joergenfriis/Steam-Engine-Simulator/Execute/damptabel.py

# damptabel.py
#
# Damptabel = [p (bar abs), tm (0C), v" (m3/kg), h' (kJ/kg), h" (kJ/kg)] (SI)
#
# Joergen Friis 25.01.2018
#########################################################################

damptabel = [
    [0.01, 6.9, 129.2, 29.34, 2514.4],
    [0.02, 17.5, 67.01, 73.46, 2533.6],
    [0.04, 28.9, 34.80, 121.41, 2554.5],
    [0.06, 36.2, 23.74, 151.50, 2567.5],
    [0.08, 41.5, 18.10, 173.86, 2577.1],
    [0.1, 45.8, 14.67, 191.83, 2584.8],
    [0.12, 49.4, 12.36, 206.94, 2591.2],
    [0.15, 54.0, 10.02, 225.97, 2599.2],
    [0.2, 60.1, 7.650, 251.45, 2609.9],
    [0.25, 65.0, 6.204, 271.99, 2618.3],
    [0.3, 69.1, 5.229, 289.30, 2625.4],
    [0.35, 72.7, 4.786, 304.30, 2631.5],
    [0.4, 75.9, 3.993, 317.65, 2636.9],
    [0.5, 81.3, 3.240, 340.56, 2646.0],
    [0.6, 85.9, 2.732, 359.93, 2653.6],
    [0.7, 90.0, 2.365, 376.77, 2660.1],
    [0.8, 93.5, 2.087, 391.72, 2665.8],
    [0.9, 96.7, 1.869, 405.21, 2670.9],
    [1, 99.6, 1.694, 417.51, 2675.4],
    [1.2, 104.8, 1,428, 439.36, 2683.4],
    [1.4, 109.3, 1.236, 458.42, 2690.3],
    [1.6, 113.3, 1.091, 475.38, 2696.2],
    [1.8, 116.9, 0.9772, 490.70, 2701.5],
    [2, 120.2, 0.8854, 504.70, 2706.3],
    [2.2, 123.3, 0.8098, 517.62, 2710.6],
    [2.4, 126.1, 0.7465, 529.64, 2714.5],
    [2.6, 128.7, 0.6925, 540.87, 2718.2],
    [2.8, 131.2, 0.6460, 551.44, 2721.5],
    [3, 133.5, 0.6056, 561.43, 2724.7],
    [3.2, 135.8, 0.5700, 570.90, 2727.6],
    [3.4, 137.9, 0.5385, 579.92, 2730.3],
    [3.6, 139.9, 0.5103, 588.53, 2732.9],
    [3.8, 141.8, 0.4851, 596.77, 2735.3],
    [4, 143.6, 0.4622, 604.67, 2737.6],
    [4.2, 145.4, 0.4415, 612.27, 2739.8],
    [4.4, 147.1, 0.4226, 619.60, 2741.9],
    [4.6, 148.7, 0.4053, 626.67, 2743.9],
    [4.8, 150.3, 0.3894, 633.50, 2745.7],
    [5, 151.8, 0.3747, 640.12, 2747.5],
    [5.2, 153.3, 0.3611, 646.53, 2749.3],
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
    
dampTilstand = [
    [0.01, 6.9, 0],
    [0.02, 17.5, 0],
    [0.04, 28.9, 0],
    [0.06, 36.2, 0],
    [0.08, 41.5, 0],
    [0.1, 45.8, 0],
    [0.12, 49.4, 0],
    [0.15, 54.0, 0],
    [0.2, 60.1, 0],
    [0.25, 65.0, 0],
    [0.3, 69.1, 0],
    [0.35, 72.7, 0],
    [0.4, 75.9, 0],
    [0.5, 81.3, 0],
    [0.6, 85.9, 0],
    [0.7, 90.0, 0],
    [0.8, 93.5, 0],
    [0.9, 96.7, 0],
    [1, 99.6, 0],
    [1.2, 104.8, 0],
    [1.4, 109.3, 0],
    [1.6, 113.3, 0],
    [1.8, 116.9, 0],
    [2, 120.2, 0],
    [2.2, 123.3, 0],
    [2.4, 126.1, 0],
    [2.6, 128.7, 0],
    [2.8, 131.2, 0],
    [3, 133.5, 0],
    [3.2, 135.8, 0],
    [3.4, 137.9, 0],
    [3.6, 139.9, 0],
    [3.8, 141.8, 0],
    [4, 143.6, 0],
    [4.2, 145.4, 0],
    [4.4, 147.1, 0],
    [4.6, 148.7, 0],
    [4.8, 150.3, 0],
    [5, 151.8, 0],
    [5.2, 153.3, 0],
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

def interpol(x1, y1, x2, x3, y3):
    y2 = ((x2-x1)*(y3-y1)/(x3-x1))+y1
    return y2
